LaskaKit/Weather_Station_Mini/img/3.jpg

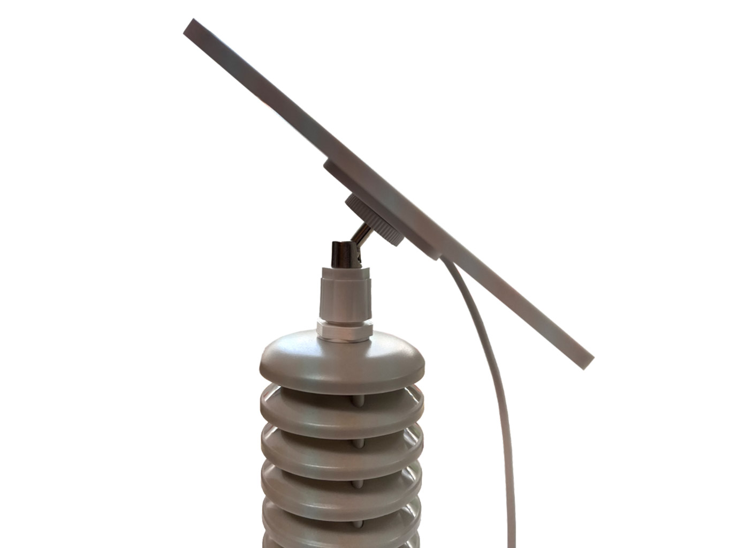
img/3.jpg
